MauArg/weather-station-station-iot/PCB/Main 1.4/Intento2/Main PCB - Estación Meteorológica - IoT_v1.4_etch_silk_top.pdf

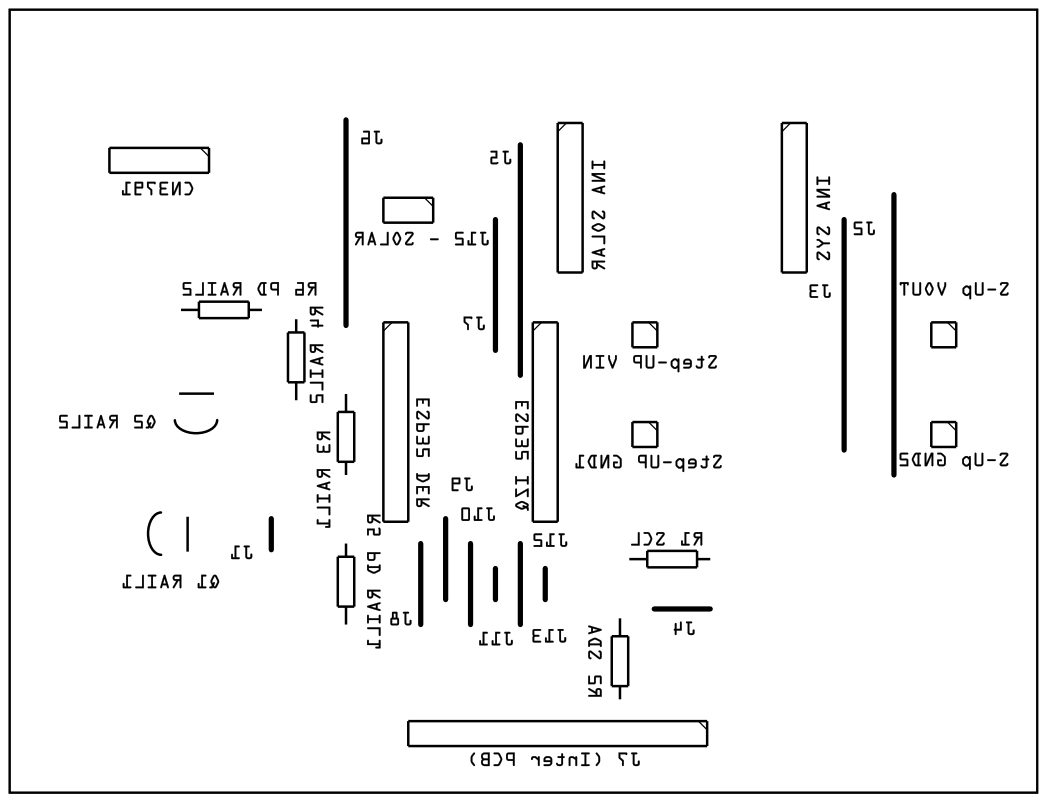
[picture p14: page 1]
