MauArg/weather-station-station-iot/src/command.h

#pragma once
#include <Arduino.h>
#include <ArduinoJson.h>

// ─── Command types ────────────────────────────────────────────────────────────
// Extensible: add here and in parseCommand()
enum class CommandType {
    NONE,
    MAINTENANCE,   // service mode: suspends sleep, starts ArduinoOTA
    REBOOT,        // clean restart
    CONFIG,        // changes runtime parameters (e.g. sleep interval)
    CALIBRATE,     // forces a calibration routine
    PING,          // responds with status without altering the cycle
    LOG,           // turns the runtime logging system on/off
    LIVE           // stops sleeping and publishes continuously while there is surplus
};

// ─── Command payload ──────────────────────────────────────────────────────────
// Example JSON on MQTT:
// {"cmd":"maintenance","timeout_min":15,"issued_at":"2026-03-24T10:00:00Z"}
// {"cmd":"config","params":{"sleep_interval_sec":60}}
// {"cmd":"reboot"}
// {"cmd":"ping"}
// {"cmd":"log_on","level":2,"entries":768}   — level 0 turns it off
// {"cmd":"live","interval_sec":5,"timeout_min":60}
// {"cmd":"live","interval_sec":5,"timeout_min":15,"force":true}  — test, ignores the sun floor
struct Command {
    CommandType type        = CommandType::NONE;
    int         timeout_min = 0;          // for MAINTENANCE and LIVE
    uint8_t     log_level   = 0;          // for LOG — 0=off, 1=anomalies, 2=summary, 3=verbose
    uint16_t    log_entries = 0;          // for LOG — 0 = full compiled-in capacity
    uint16_t    live_interval_sec = 0;    // for LIVE — seconds between publishes
    bool        live_force        = false;// for LIVE — skip the sun floor (testing only)
    String      raw;                      // raw payload for further processing
    bool        valid       = false;
};

Command     parseCommand(const String& json);
const char* commandTypeToString(CommandType type);
