MauArg/weather-station-station-iot/src/board_config.h

// #ifndef BOARD_CONFIG_H
// #define BOARD_CONFIG_H

// #define BOARD_ESP32C3_SUPERMINI

// #ifdef BOARD_ESP32C3_SUPERMINI
//   // LED
//   #define LED_BUILTIN 8
  
//   // I2C for BMP180
//   #define I2C_SDA 4
//   #define I2C_SCL 5
  
//   // DHT22
//   #define DHT22_PIN 2
  
//   // Battery monitoring (Phase 2)
//   #define BATTERY_ADC_PIN 0
//   #define BATTERY_VOLTAGE_DIVIDER 2.0
//   #define HAS_BATTERY_CHARGER false
  
//   // Battery thresholds
//   #define BATTERY_CRITICAL_MV 3000
//   #define BATTERY_LOW_MV 3400
//   #define BATTERY_NORMAL_MV 3800
// #endif

// #endif
